zuzu59/bubblemeter/bubblemter1/zTemperatureBubblemter1.h

// zf240611.1035

// ATTENTION, version special pour le Bubblemter1 !    (zf240608.1202)
// car le DS18B20 est alimenté directement depuis les VCC et GND du esp32-c3


// Temperature sensor DS18B20
#include <OneWire.h>
#include <DallasTemperature.h>

// ATTENTION, c'est le brochage alimenté directement depuis les VCC et GND du esp32-c3 !
// const int vccPin = 1;       // the number of the VCC pin
const int pullupPin = 2;    // the number of the PULLUP pin
const int oneWireBus = 1;   // GPIO where the DS18B20 is connected to
// const int gndPin = 4;       // the number of the GND pin
// Setup a oneWire instance to communicate with any OneWire devices
OneWire oneWire(oneWireBus);
// Pass our oneWire reference to Dallas Temperature sensor 
DallasTemperature sensors(&oneWire);


// Temperature sensor DS18B20 initialising
void initDS18B20Sensor(){
    // pinMode(gndPin, OUTPUT);   // gnd
    // digitalWrite(gndPin, LOW);
    pinMode(pullupPin, INPUT_PULLUP);   // pull up
    // pinMode(vccPin, OUTPUT );   // vcc
    // digitalWrite(vccPin, HIGH);
    // Start the DS18B20 sensor
    sensors.begin();
}


RTC_DATA_ATTR float tempInternal1 = 0;
RTC_DATA_ATTR float tempInternal2 = 0;


// Lit les senseurs
void readSensor(){
    // // lit la température interne
    // sensorValue1 = temperatureRead();
    // sensorValue1 = sensorValue1 - 8.0;        // Enlève des ° en trop, je ne sais pas pourquoi ? zf240526.1142, zf240530.0908

    // // moyenne glissante
    // sensorValue1 = (sensorValue1 + tempInternal1 + tempInternal2) / 3;
    // tempInternal1 = tempInternal2;
    // tempInternal2 = sensorValue1;

    // lit la température du DS18B20
    sensors.requestTemperatures(); 
    sensorValue5 = sensors.getTempCByIndex(0);
}
