zuzu59/bubblemeter/bubblemter1/zsolarpulse.h

//zf240525.1038

// Machine à état pour faire pulser deux fois la petite LED sans bloquer le système
void sonarPulse(){
  if (zSonarPulseNextMillis < millis()){
    switch (zSonarPulseState){
      // 1ère pulse allumée que l'on doit éteindre !
      case 1:
        digitalWrite(ledPin, HIGH);
        zSonarPulseNextMillis = millis() + zSonarPulseOff;
        zSonarPulseState = 2;
        break;
      // 1ère pulse éteinte que l'on doit allumer !
      case 2:
        digitalWrite(ledPin, LOW);
        zSonarPulseNextMillis = millis() + zSonarPulseOn;
        zSonarPulseState = 3;
        break;
      // 2e pulse allumée que l'on doit éteindre et attendre le wait !
      case 3:
        digitalWrite(ledPin, HIGH);
        zSonarPulseNextMillis = millis() + zSonarPulseWait;
        zSonarPulseState = 4;
        break;
      // 2e pulse éteinte pendant le wait que l'on doit allumer !
      case 4:
        digitalWrite(ledPin, LOW);
        zSonarPulseNextMillis = millis() + zSonarPulseOn;
        zSonarPulseState = 1;
        break;
    }
  }
}
